K4iwer/Spilling/Aplicação/assets/imagens/emocao/assustado.png

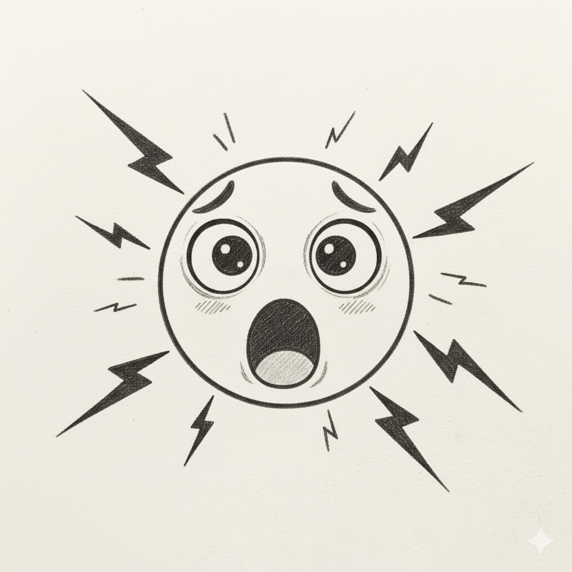
Aplicação/assets/imagens/emocao/assustado.png
