K4iwer/Spilling/Aplicação/assets/imagens/emocao/bravo.png

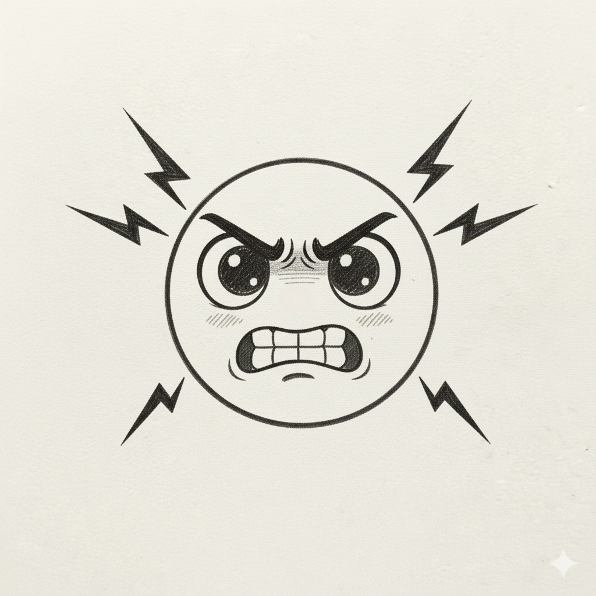
Aplicação/assets/imagens/emocao/bravo.png
