K4iwer/Spilling/Aplicação/assets/imagens/emocao/feliz.png

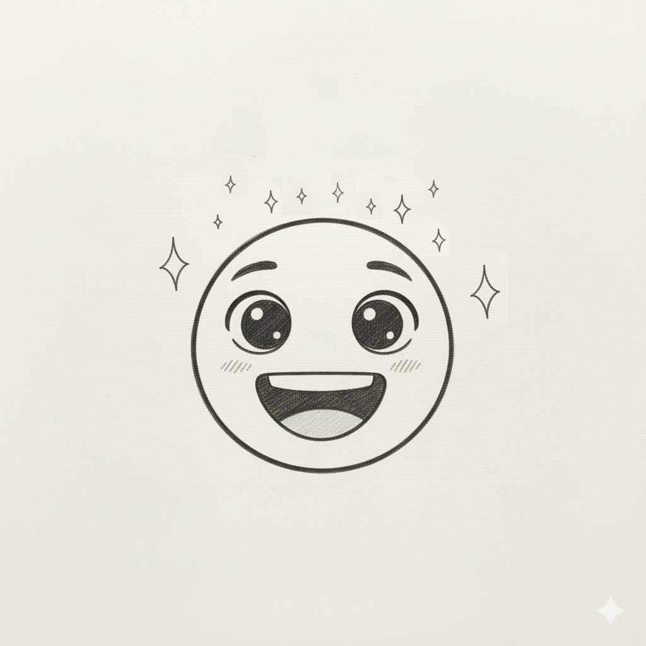
Aplicação/assets/imagens/emocao/feliz.png
