K4iwer/Spilling/Aplicação/assets/imagens/emocao/triste.png

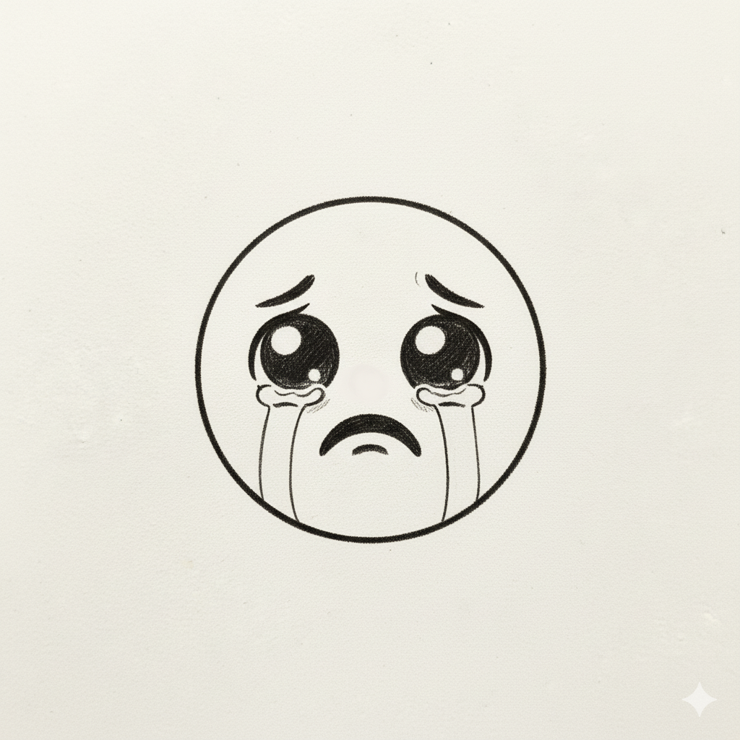
Aplicação/assets/imagens/emocao/triste.png
