K4iwer/Spilling/Aplicação/assets/imagens/fases/fase1.png

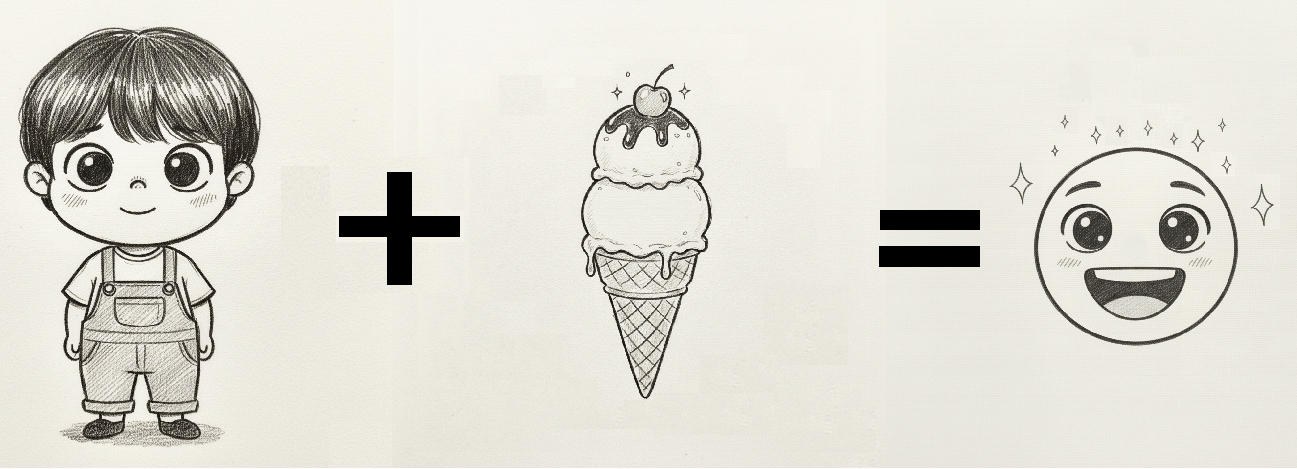
Aplicação/assets/imagens/fases/fase1.png
