K4iwer/Spilling/Aplicação/assets/imagens/fases/fase2.png

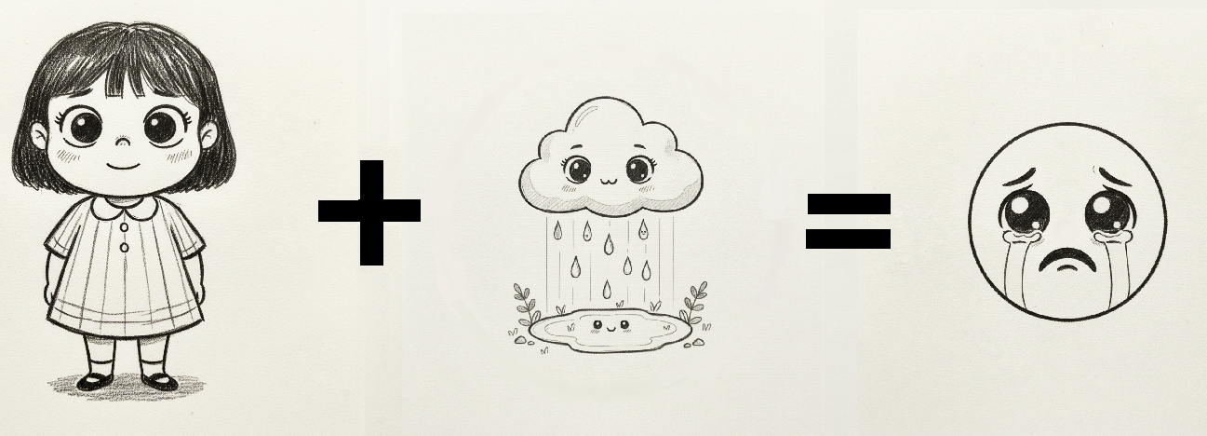
Aplicação/assets/imagens/fases/fase2.png
