K4iwer/Spilling/Aplicação/assets/imagens/fases/fase3.png

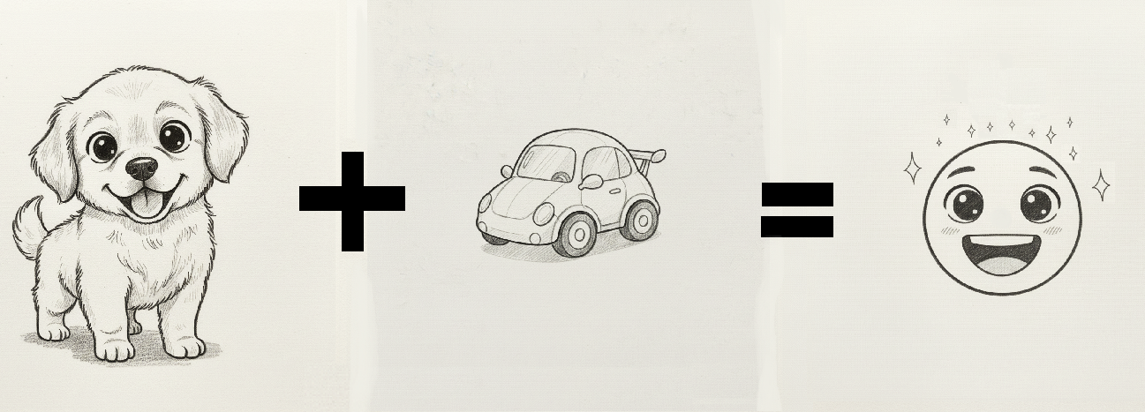
Aplicação/assets/imagens/fases/fase3.png
