K4iwer/Spilling/Aplicação/assets/imagens/fases/fase5.png

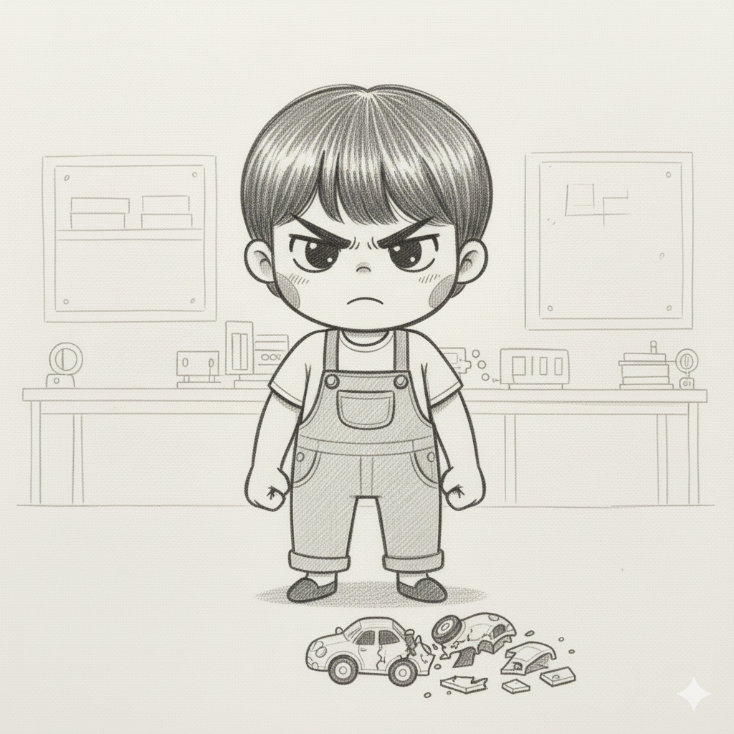
Aplicação/assets/imagens/fases/fase5.png
