K4iwer/Spilling/Aplicação/assets/imagens/fases/fase8.png

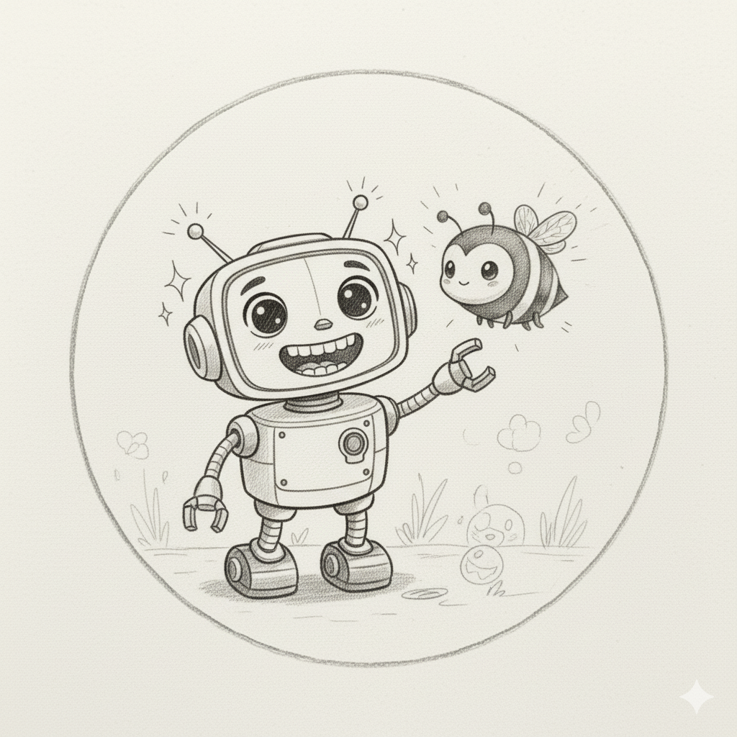
Aplicação/assets/imagens/fases/fase8.png
