K4iwer/Spilling/Aplicação/assets/imagens/fases/fase10.png

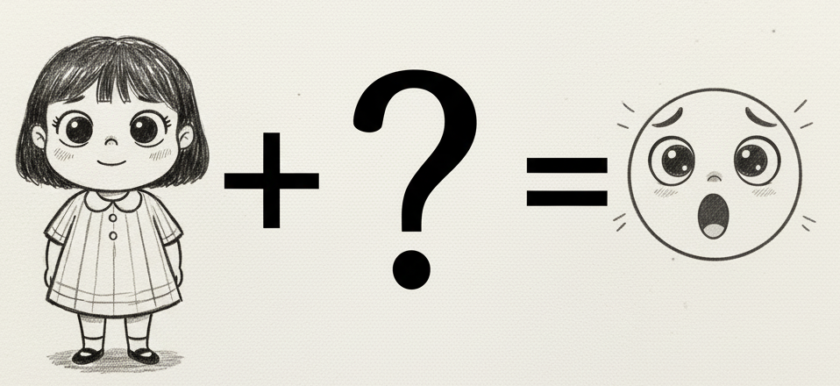
Aplicação/assets/imagens/fases/fase10.png
