K4iwer/Spilling/Aplicação/assets/imagens/fases/fase11.png

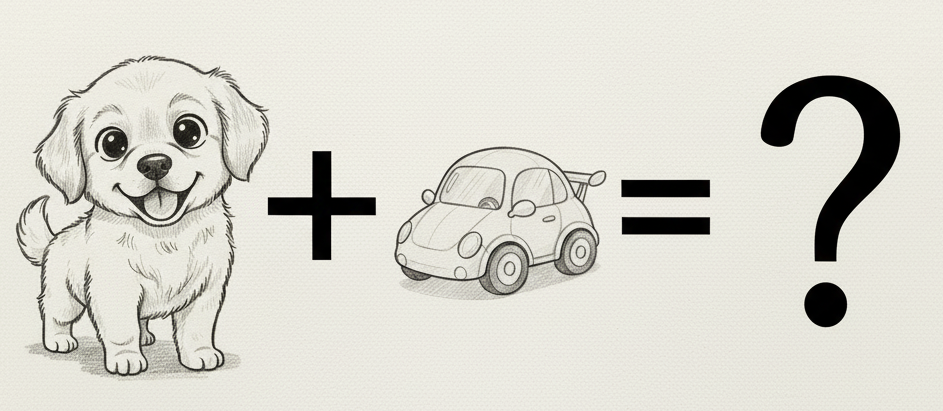
Aplicação/assets/imagens/fases/fase11.png
