K4iwer/Spilling/Aplicação/assets/imagens/fases/fase12.png

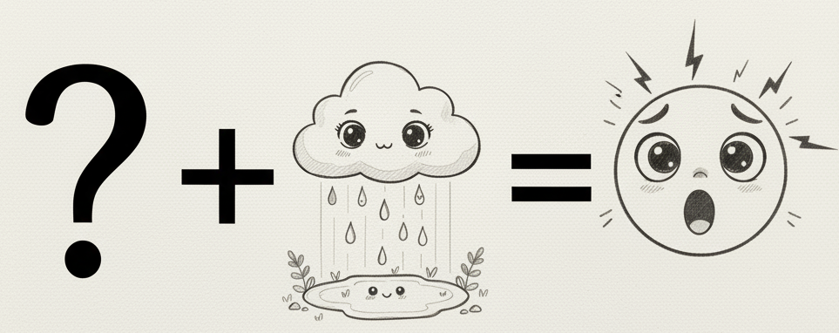
Aplicação/assets/imagens/fases/fase12.png
