K4iwer/Spilling/Aplicação/assets/imagens/feedback/acertou.png

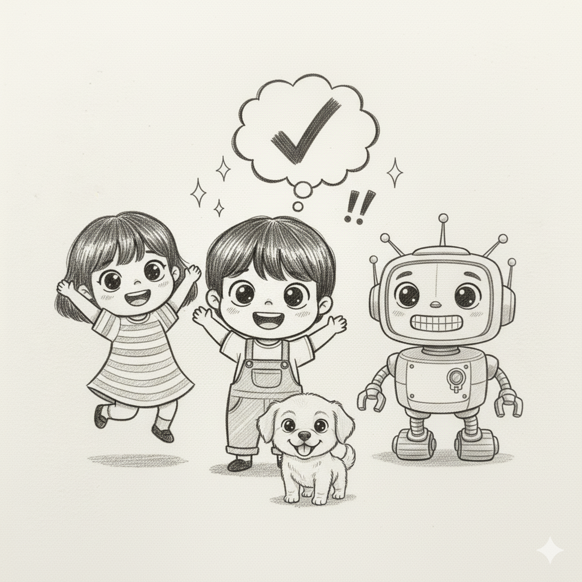
Aplicação/assets/imagens/feedback/acertou.png
