K4iwer/Spilling/Aplicação/assets/imagens/feedback/errou.png

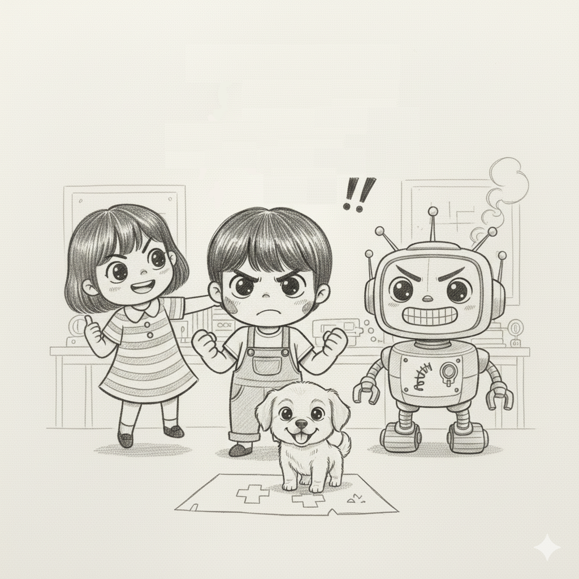
Aplicação/assets/imagens/feedback/errou.png
