K4iwer/Spilling/Aplicação/assets/imagens/feedback/vitoria.png

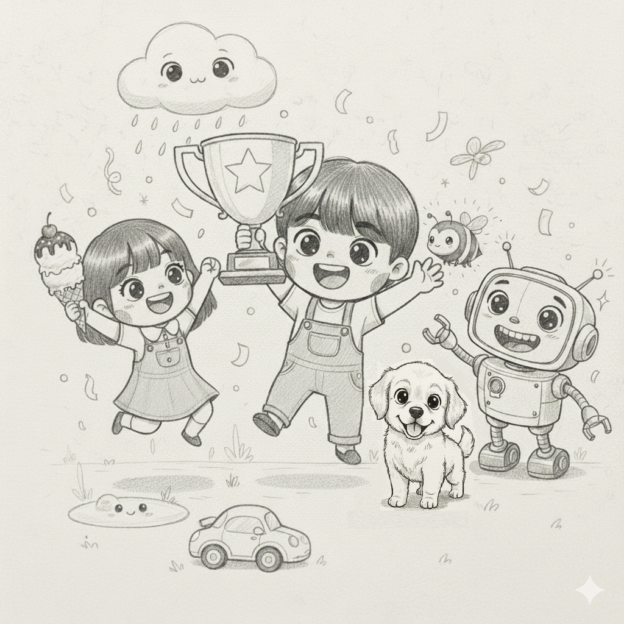
Aplicação/assets/imagens/feedback/vitoria.png
