K4iwer/Spilling/Aplicação/assets/imagens/personagens/cachorro.png

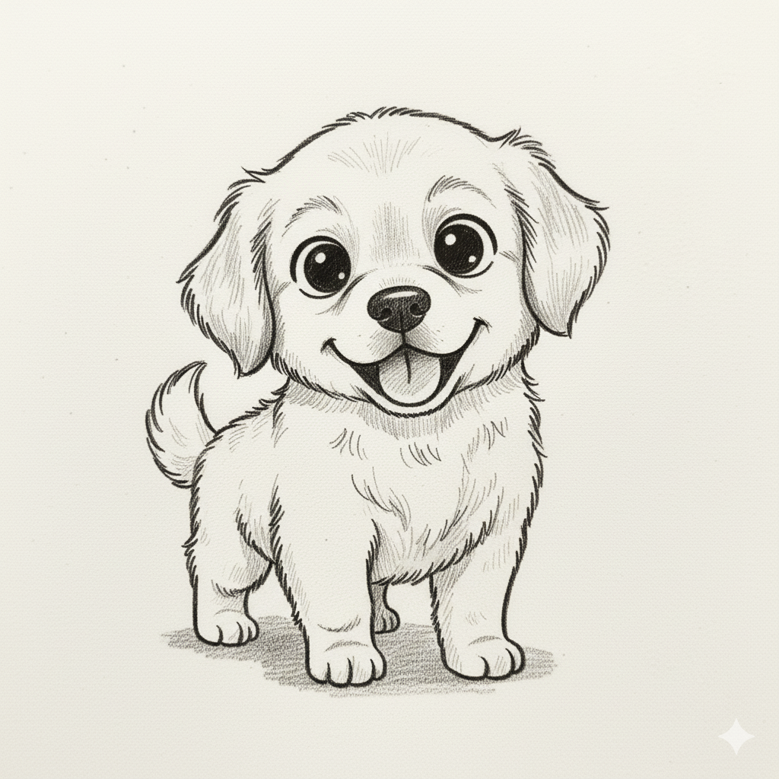
Aplicação/assets/imagens/personagens/cachorro.png
