K4iwer/Spilling/Aplicação/assets/imagens/personagens/menino.png

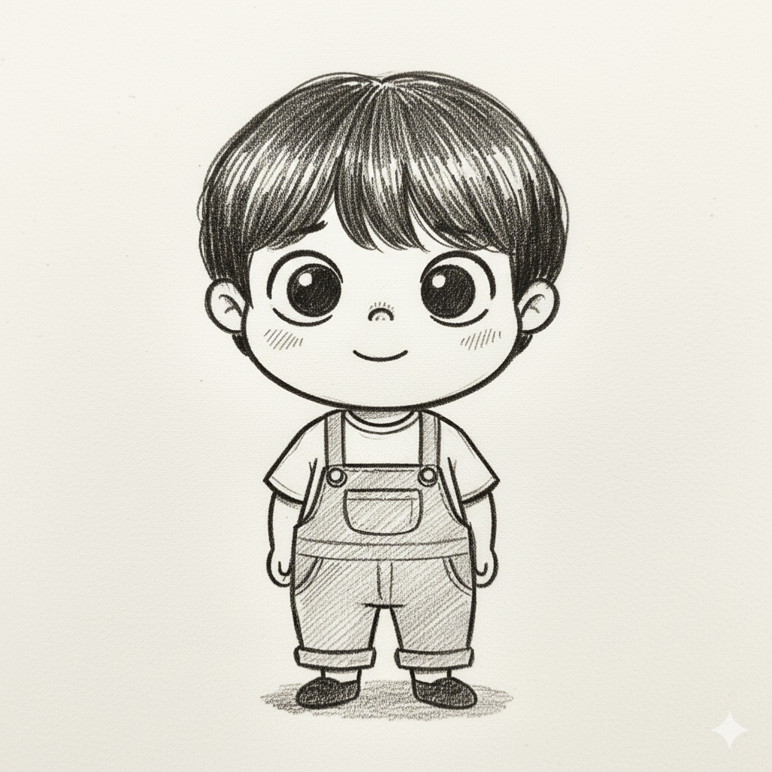
Aplicação/assets/imagens/personagens/menino.png
