K4iwer/Spilling/Aplicação/assets/imagens/personagens/robo.png

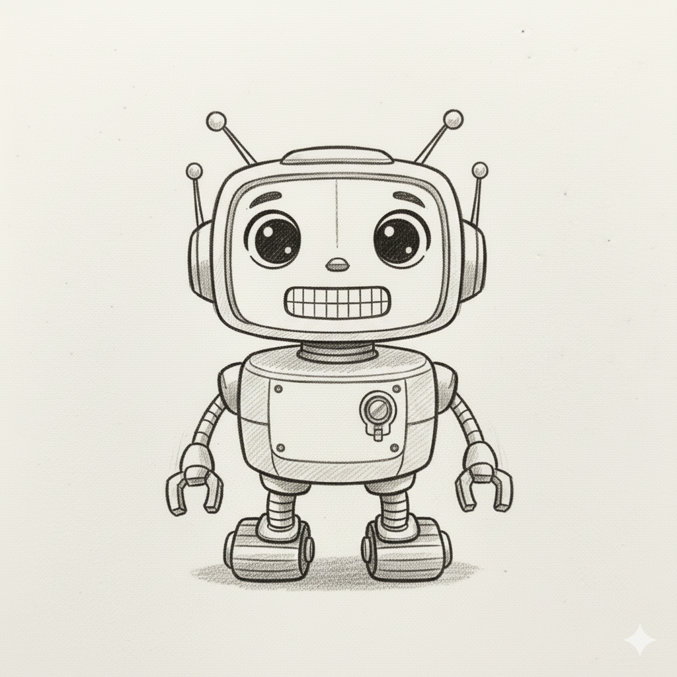
Aplicação/assets/imagens/personagens/robo.png
