K4iwer/Spilling/Aplicação/assets/imagens/situacao/abelha.png

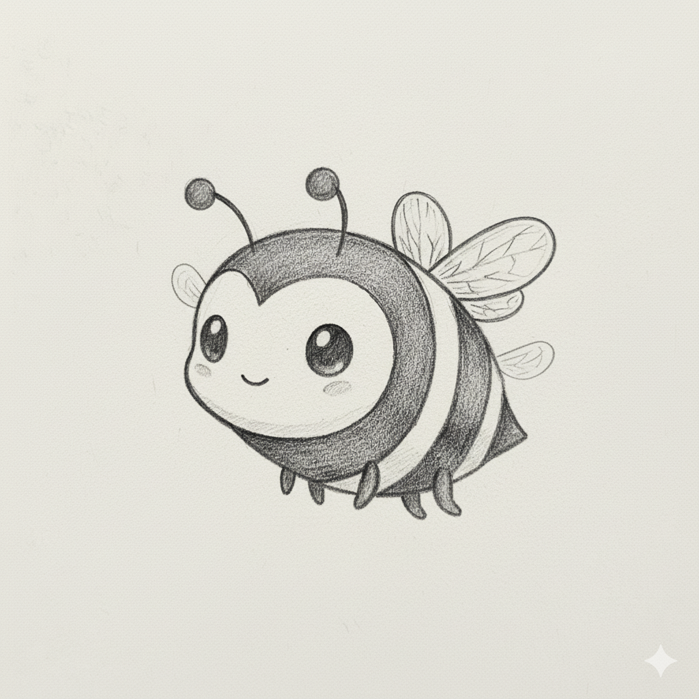
Aplicação/assets/imagens/situacao/abelha.png
