K4iwer/Spilling/Aplicação/assets/imagens/situacao/carro.png

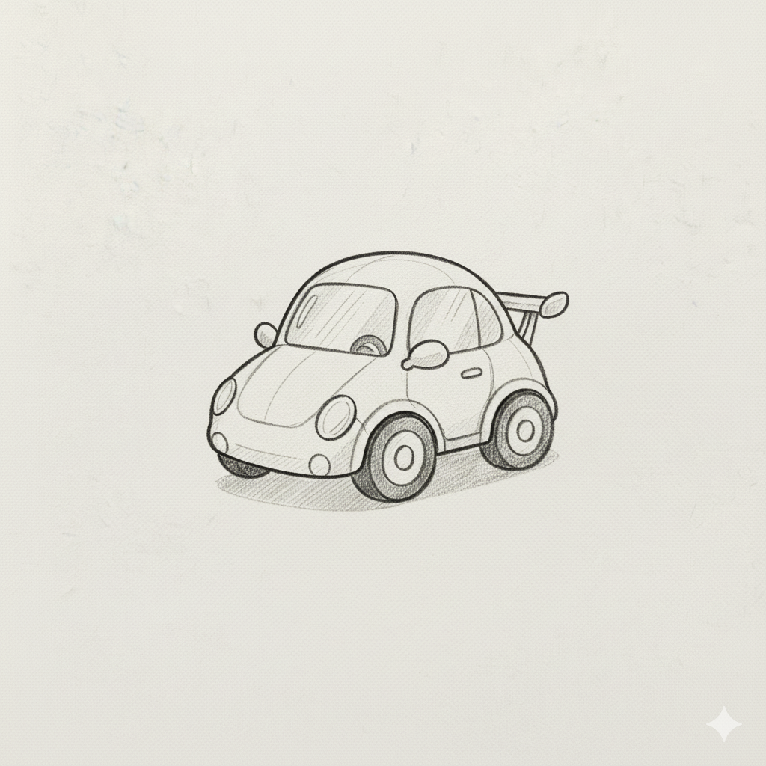
Aplicação/assets/imagens/situacao/carro.png
