K4iwer/Spilling/Aplicação/assets/imagens/situacao/chuva.png

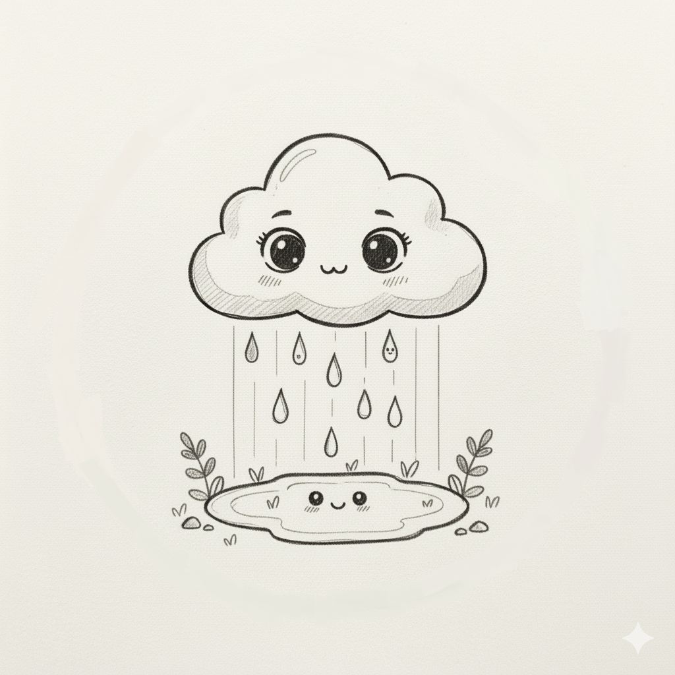
Aplicação/assets/imagens/situacao/chuva.png
