K4iwer/Spilling/Documentos/Imagens/Vista_lateral.jpeg

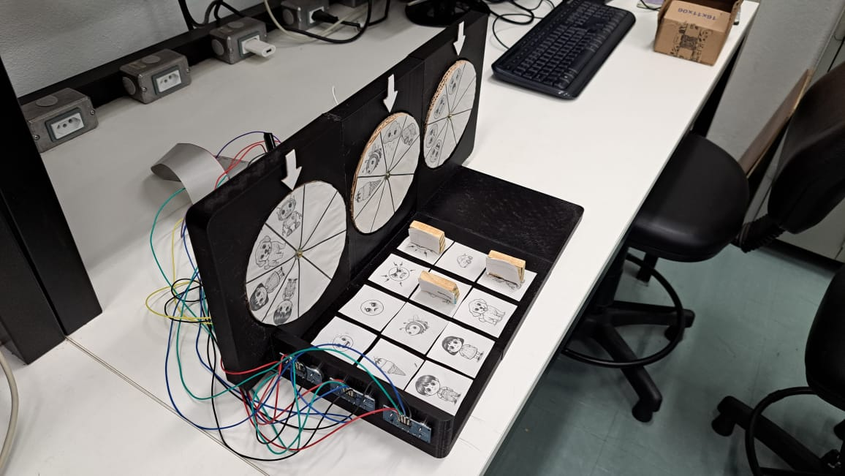
Documentos/Imagens/Vista_lateral.jpeg
