K4iwer/Spilling/Documentos/Imagens/Vista_traseira.jpeg

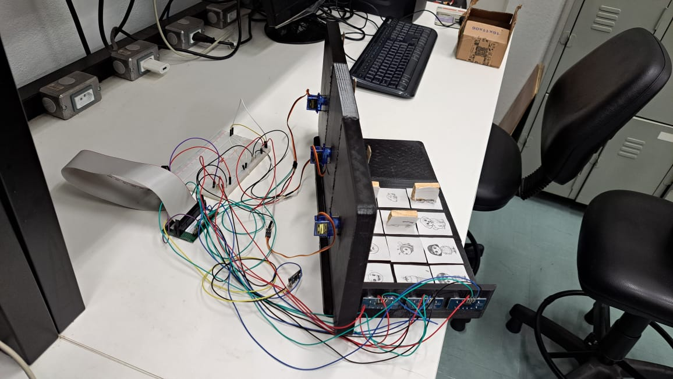
Documentos/Imagens/Vista_traseira.jpeg
